matheusvps/resistor-wizard/Documentation/PCB.png

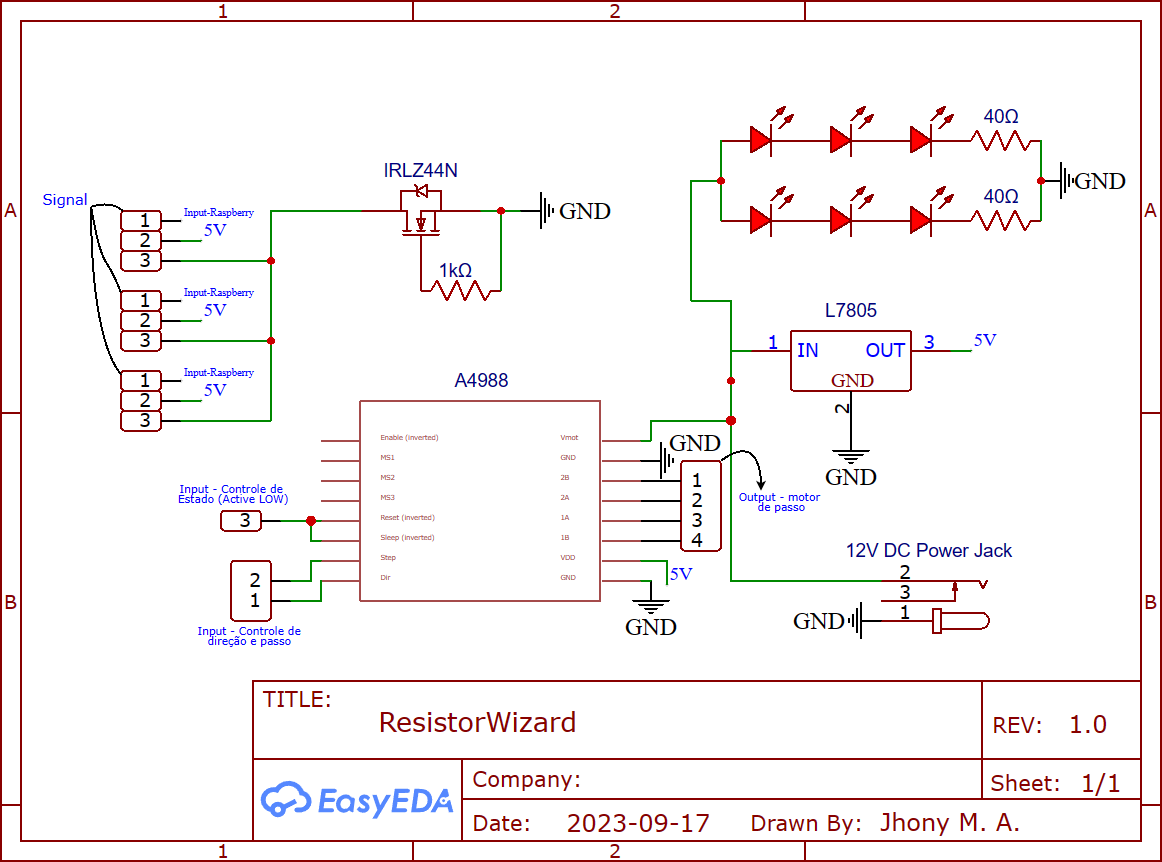
Documentation/PCB.png
