matheusvps/resistor-wizard/Documentation/PCB_v2.png

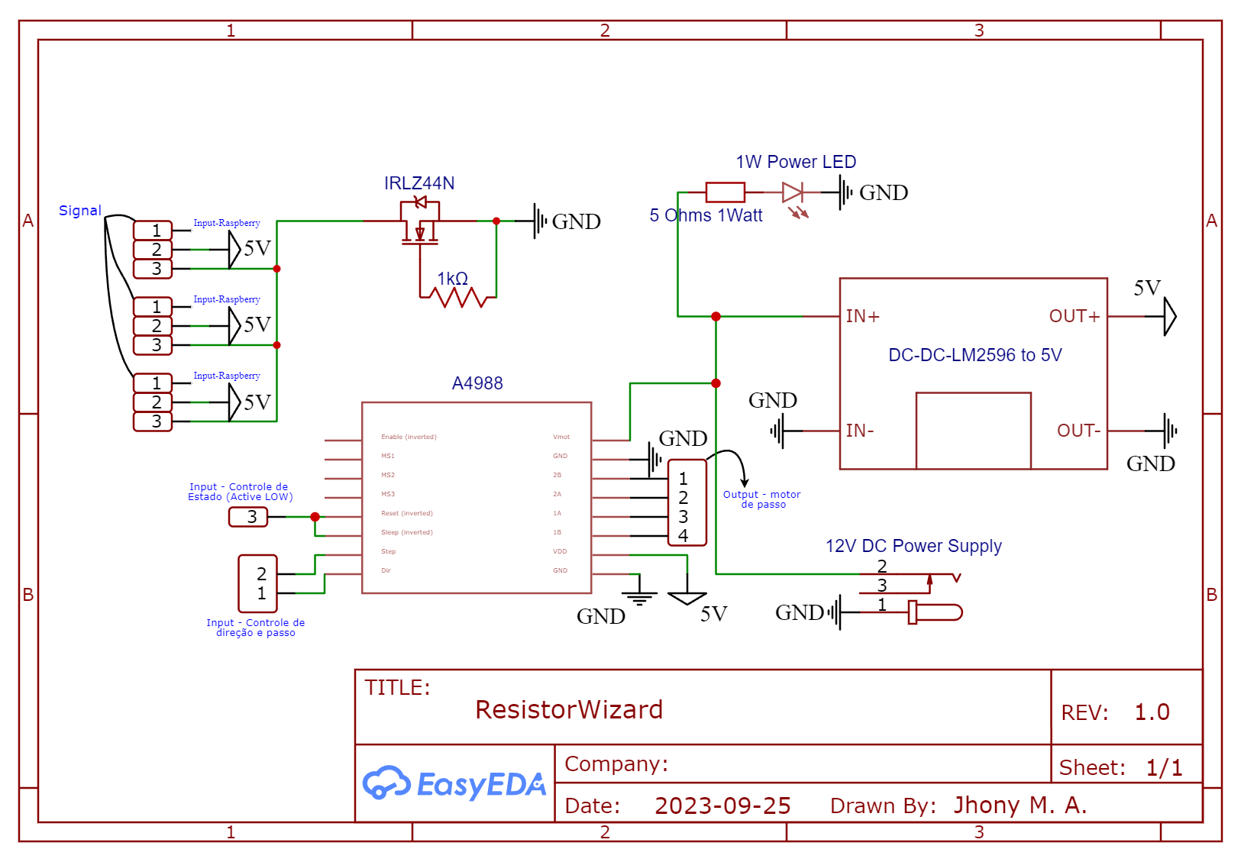
Documentation/PCB_v2.png
