matheusvps/resistor-wizard/Backend/Functionality Tests/0001.png

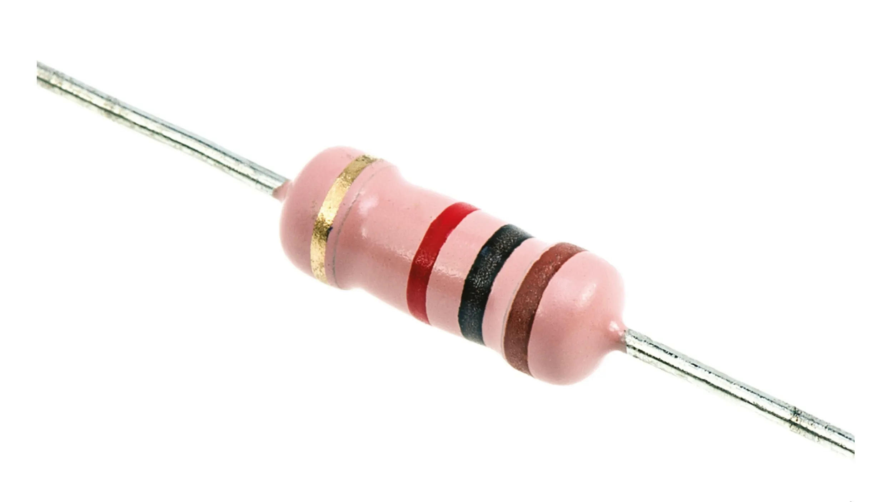
Backend/Functionality Tests/0001.png
