matheusvps/resistor-wizard/Backend/Functionality Tests/0003.jpg

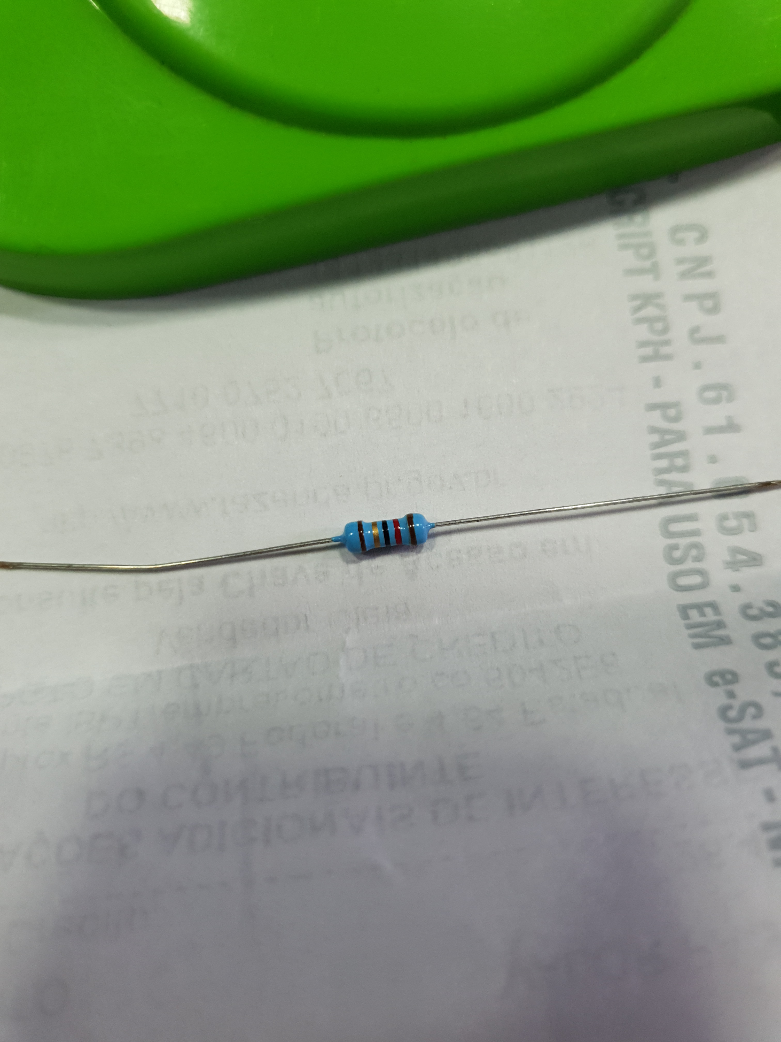
Backend/Functionality Tests/0003.jpg
