matheusvps/resistor-wizard/Backend/Functionality Tests/0004.jpg

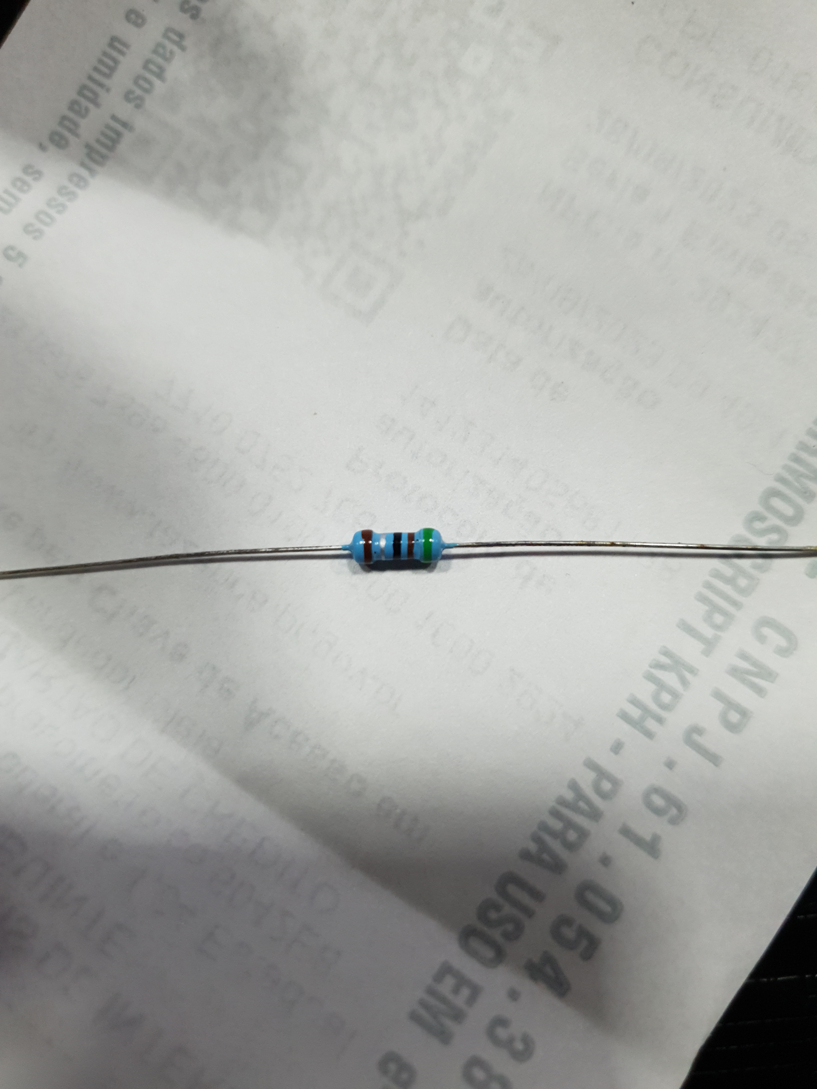
Backend/Functionality Tests/0004.jpg
