matheusvps/resistor-wizard/Backend/Functionality Tests/0005.jpg

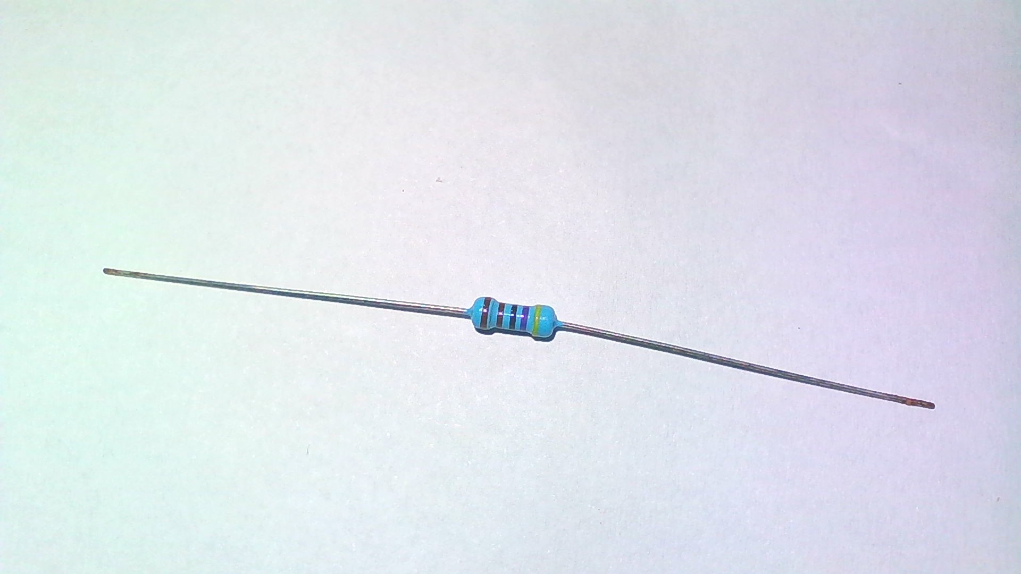
Backend/Functionality Tests/0005.jpg
