matheusvps/resistor-wizard/Backend/Functionality Tests/0008.png

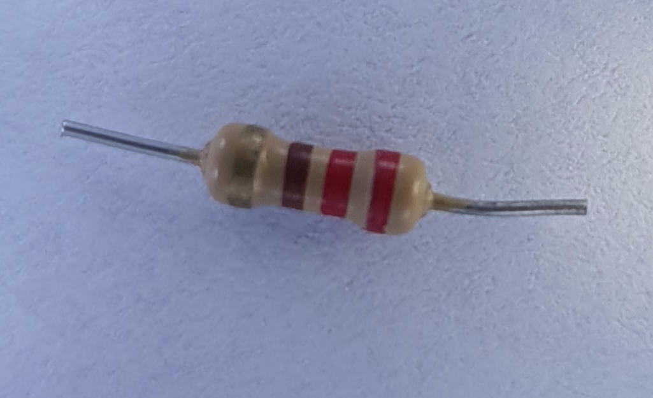
Backend/Functionality Tests/0008.png
