matheusvps/resistor-wizard/Backend/Functionality Tests/0009.png

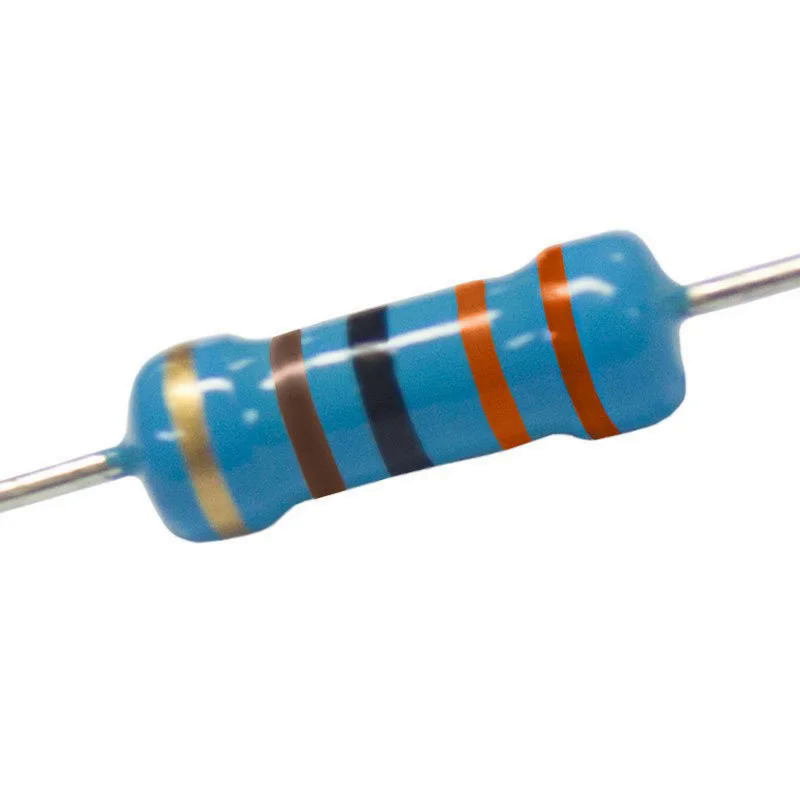
Backend/Functionality Tests/0009.png
