matheusvps/resistor-wizard/Backend/Functionality Tests/0010.png

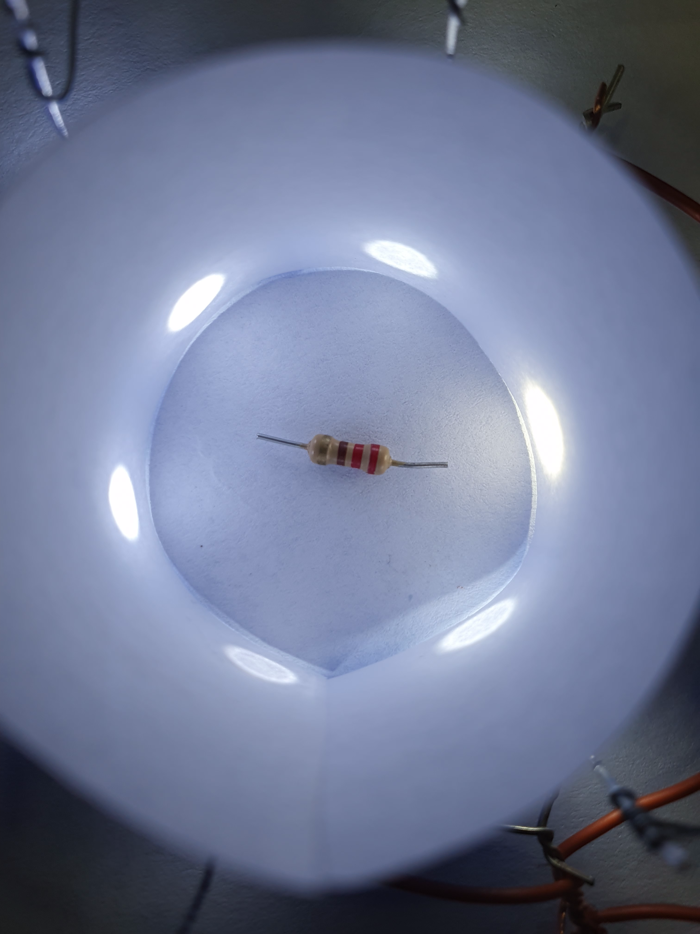
Backend/Functionality Tests/0010.png
