matheusvps/resistor-wizard/Backend/Functionality Tests/0011.png

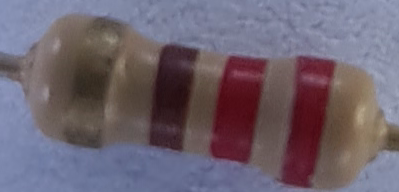
Backend/Functionality Tests/0011.png
