matheusvps/resistor-wizard/Backend/Functionality Tests/0013.jpg

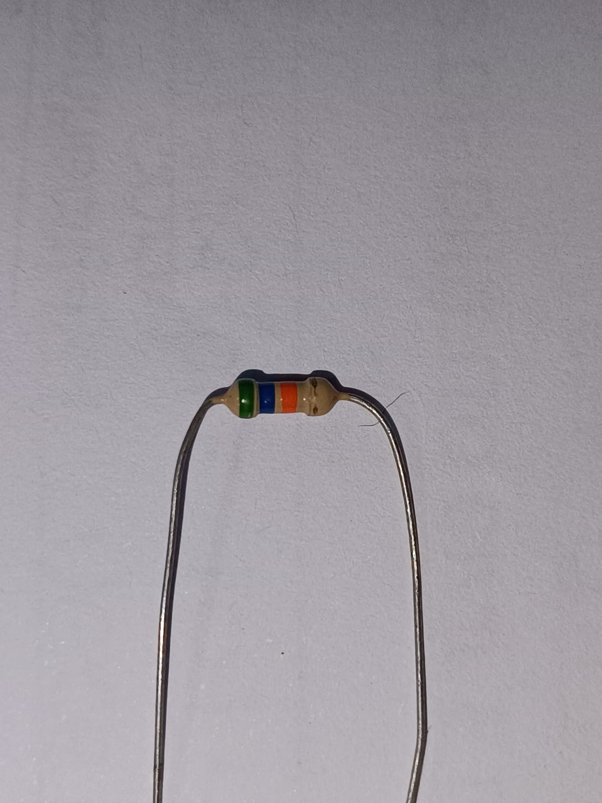
Backend/Functionality Tests/0013.jpg
