matheusvps/resistor-wizard/Backend/Functionality Tests/0014.jpg

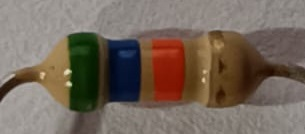
Backend/Functionality Tests/0014.jpg
