matheusvps/resistor-wizard/Backend/Functionality Tests/0016.jpg

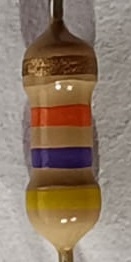
Backend/Functionality Tests/0016.jpg
