matheusvps/resistor-wizard/Backend/Functionality Tests/0017.jpg

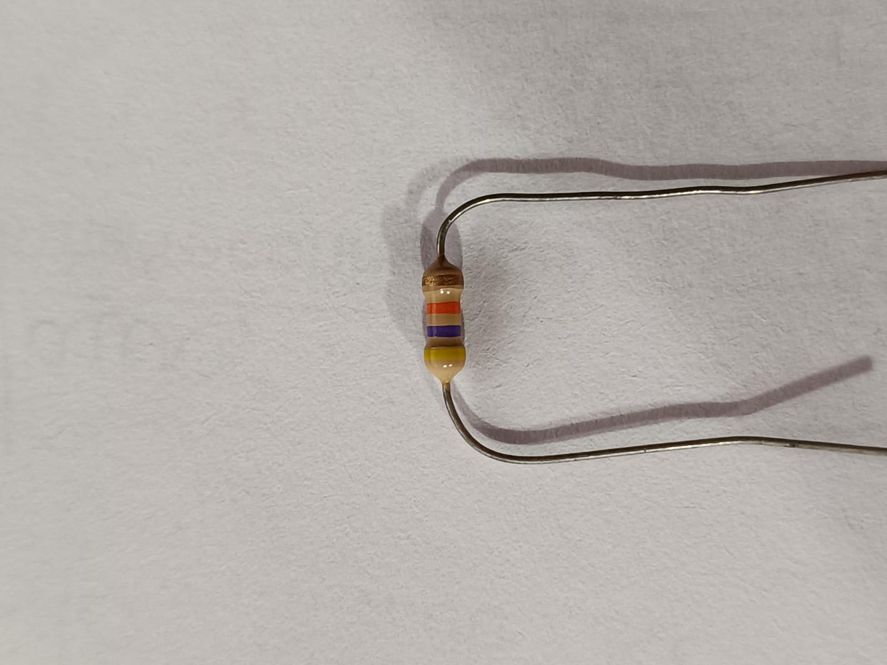
Backend/Functionality Tests/0017.jpg
