matheusvps/resistor-wizard/Backend/Functionality Tests/0018.jpg

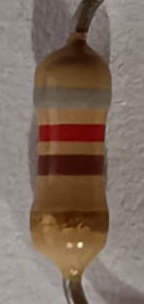
Backend/Functionality Tests/0018.jpg
