matheusvps/resistor-wizard/Backend/Functionality Tests/0019.jpg

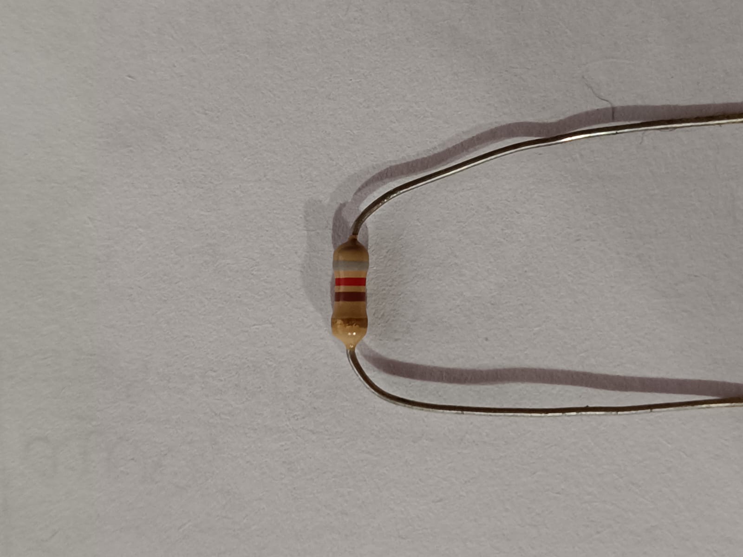
Backend/Functionality Tests/0019.jpg
