matheusvps/resistor-wizard/Backend/Functionality Tests/0020.jpg

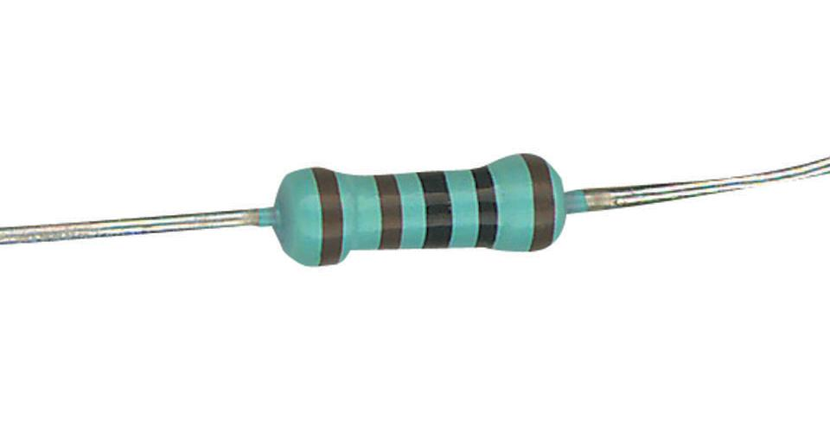
Backend/Functionality Tests/0020.jpg
