matheusvps/resistor-wizard/Backend/Functionality Tests/0021.png

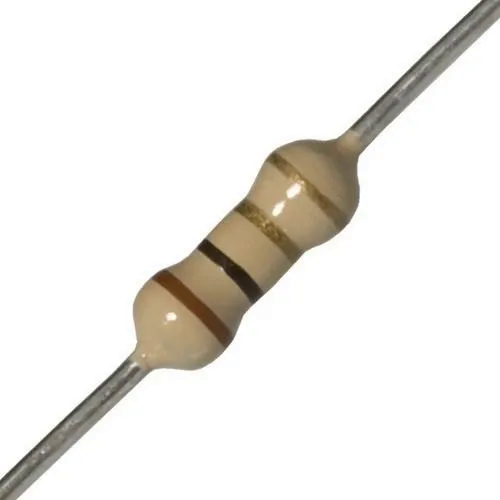
Backend/Functionality Tests/0021.png
