matheusvps/resistor-wizard/Backend/Functionality Tests/0023.jpg

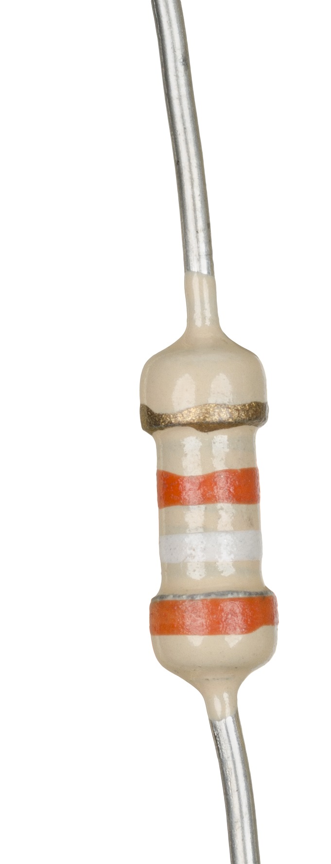
Backend/Functionality Tests/0023.jpg
