matheusvps/resistor-wizard/Backend/Functionality Tests/0024.jpg

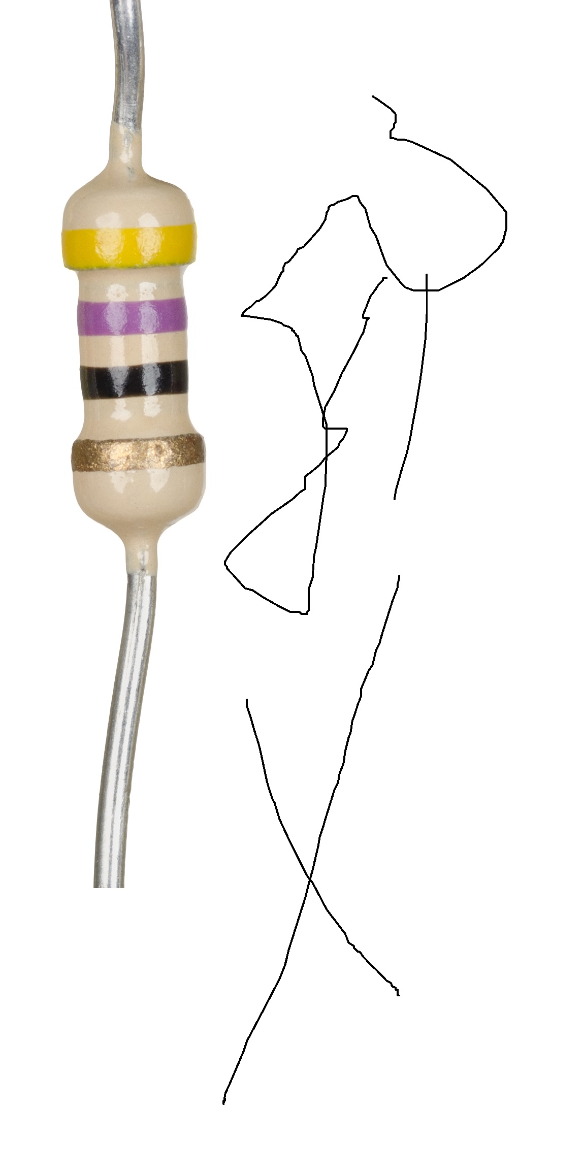
Backend/Functionality Tests/0024.jpg
