matheusvps/resistor-wizard/Backend/Functionality Tests/0025.png

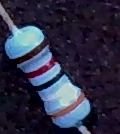
Backend/Functionality Tests/0025.png
