matheusvps/resistor-wizard/Backend/Functionality Tests/0026.jpg

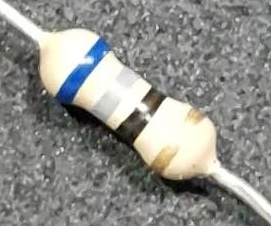
Backend/Functionality Tests/0026.jpg
