matheusvps/resistor-wizard/Backend/Functionality Tests/0027.jpg

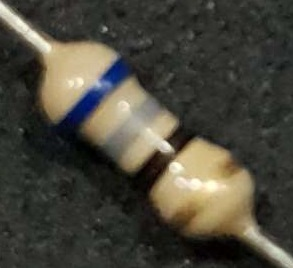
Backend/Functionality Tests/0027.jpg
