matheusvps/resistor-wizard/Documentation/Simulations/LM2596/lm2596_adj.asc

B1: bv; V=12 + (random(100000*time)-0.5)/1
C1: cap; 470µF; V=50V
C3: cap; 220µF
D1: schottky; 1N5819
D2: LED; LXHL-BW02
L1: ind; 1µH
R1: res; 1k
R2: res; 3.065k
R3: res; 10; tol=1 pwr=2
U1: LM2596_ADJ
Named nets: 0
.tran 0 4ms 0 1E-02
