matheusvps/resistor-wizard/Documentation/Simulations/LM2596/lm2596_const.asc

C1: cap; 470µF; V=50V
C2: cap; 220µF; V=35V
C3: cap; 180µF
D1: schottky; B540C
D2: LED; LXHL-BW02
L1: ind; 68µH
L2: ind; 3µH
R3: res; 5; tol=1 pwr=2
U1: LM2596_5P0_TRANS
V1: voltage; 12V
Named nets: 0
.tran 0 0.1 0 1E-02
.inc LM2596_5P0_TRANS.LIB
